aturiel/word-clock/STL/images/IMG_5544.jpg

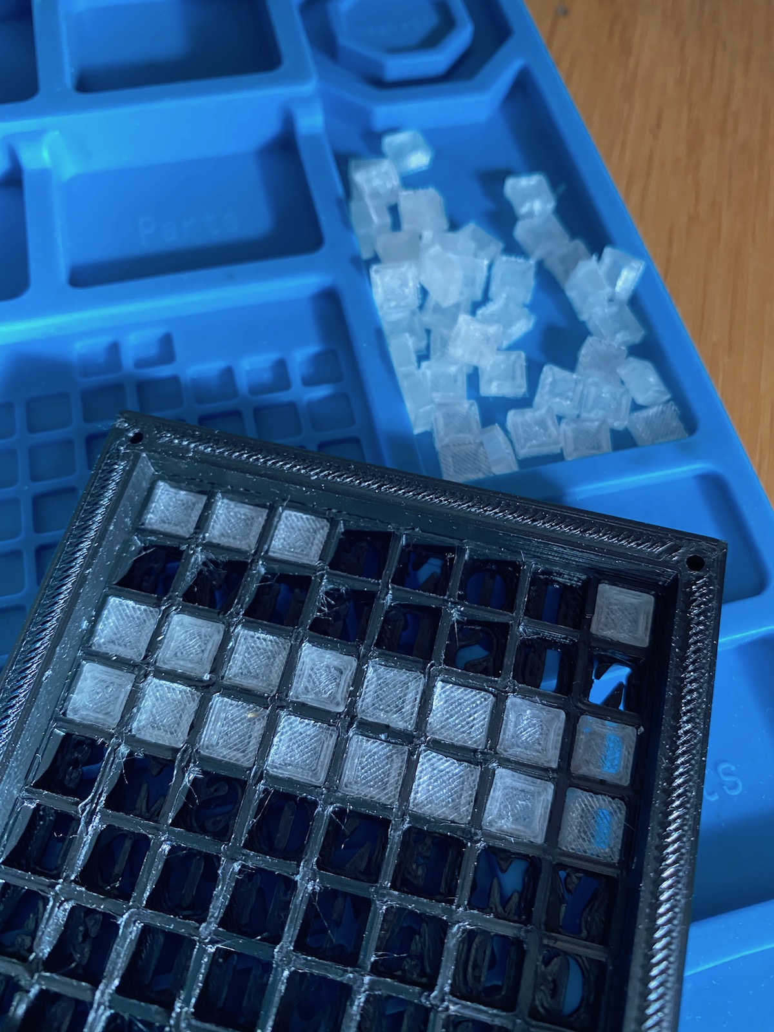
STL/images/IMG_5544.jpg
