aturiel/word-clock/STL/images/IMG_5545.jpg

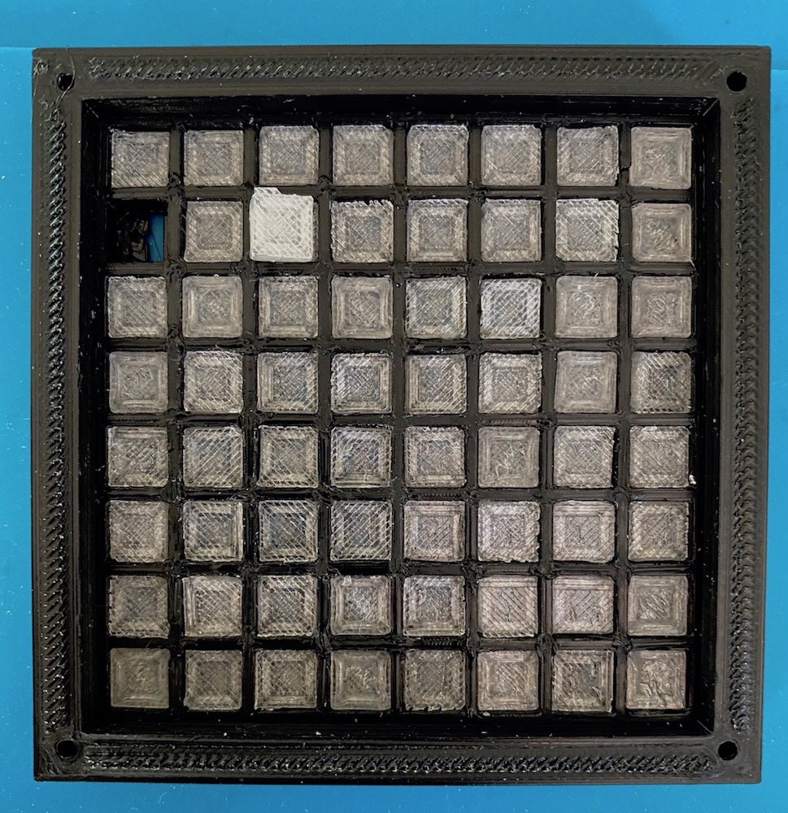
STL/images/IMG_5545.jpg
