aturiel/word-clock/STL/images/IMG_5586.jpg

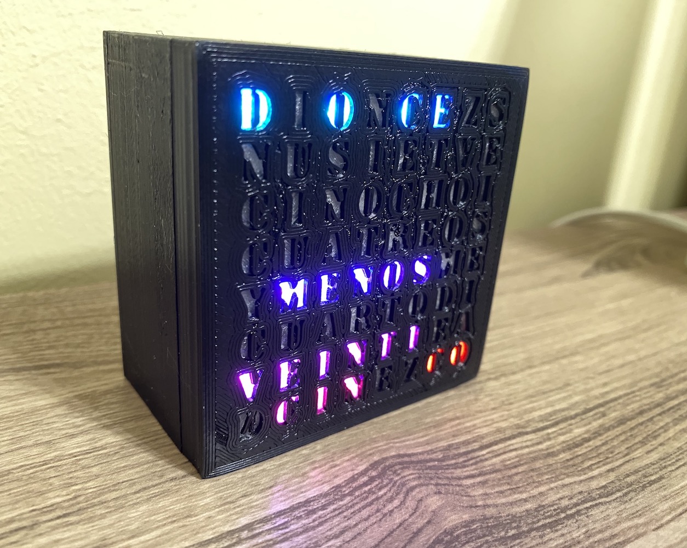
STL/images/IMG_5586.jpg
