aturiel/word-clock/STL/images/IMG_5587.jpg

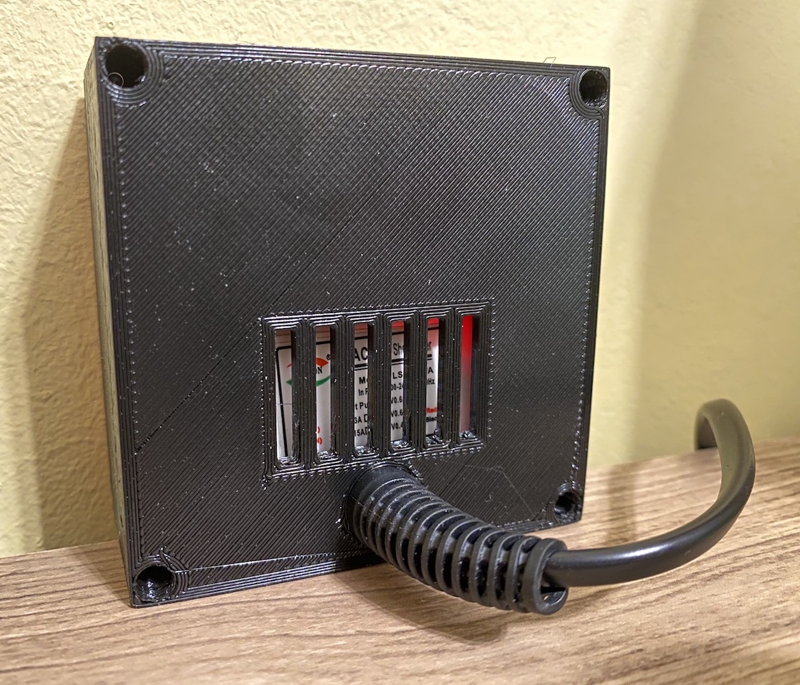
STL/images/IMG_5587.jpg
